mgd1984/boosted-remote/electrical/kicad/boosted_remote.kicad_sch

## KiCad design electrical/kicad/boosted_remote.kicad_sch (2026-04-09)

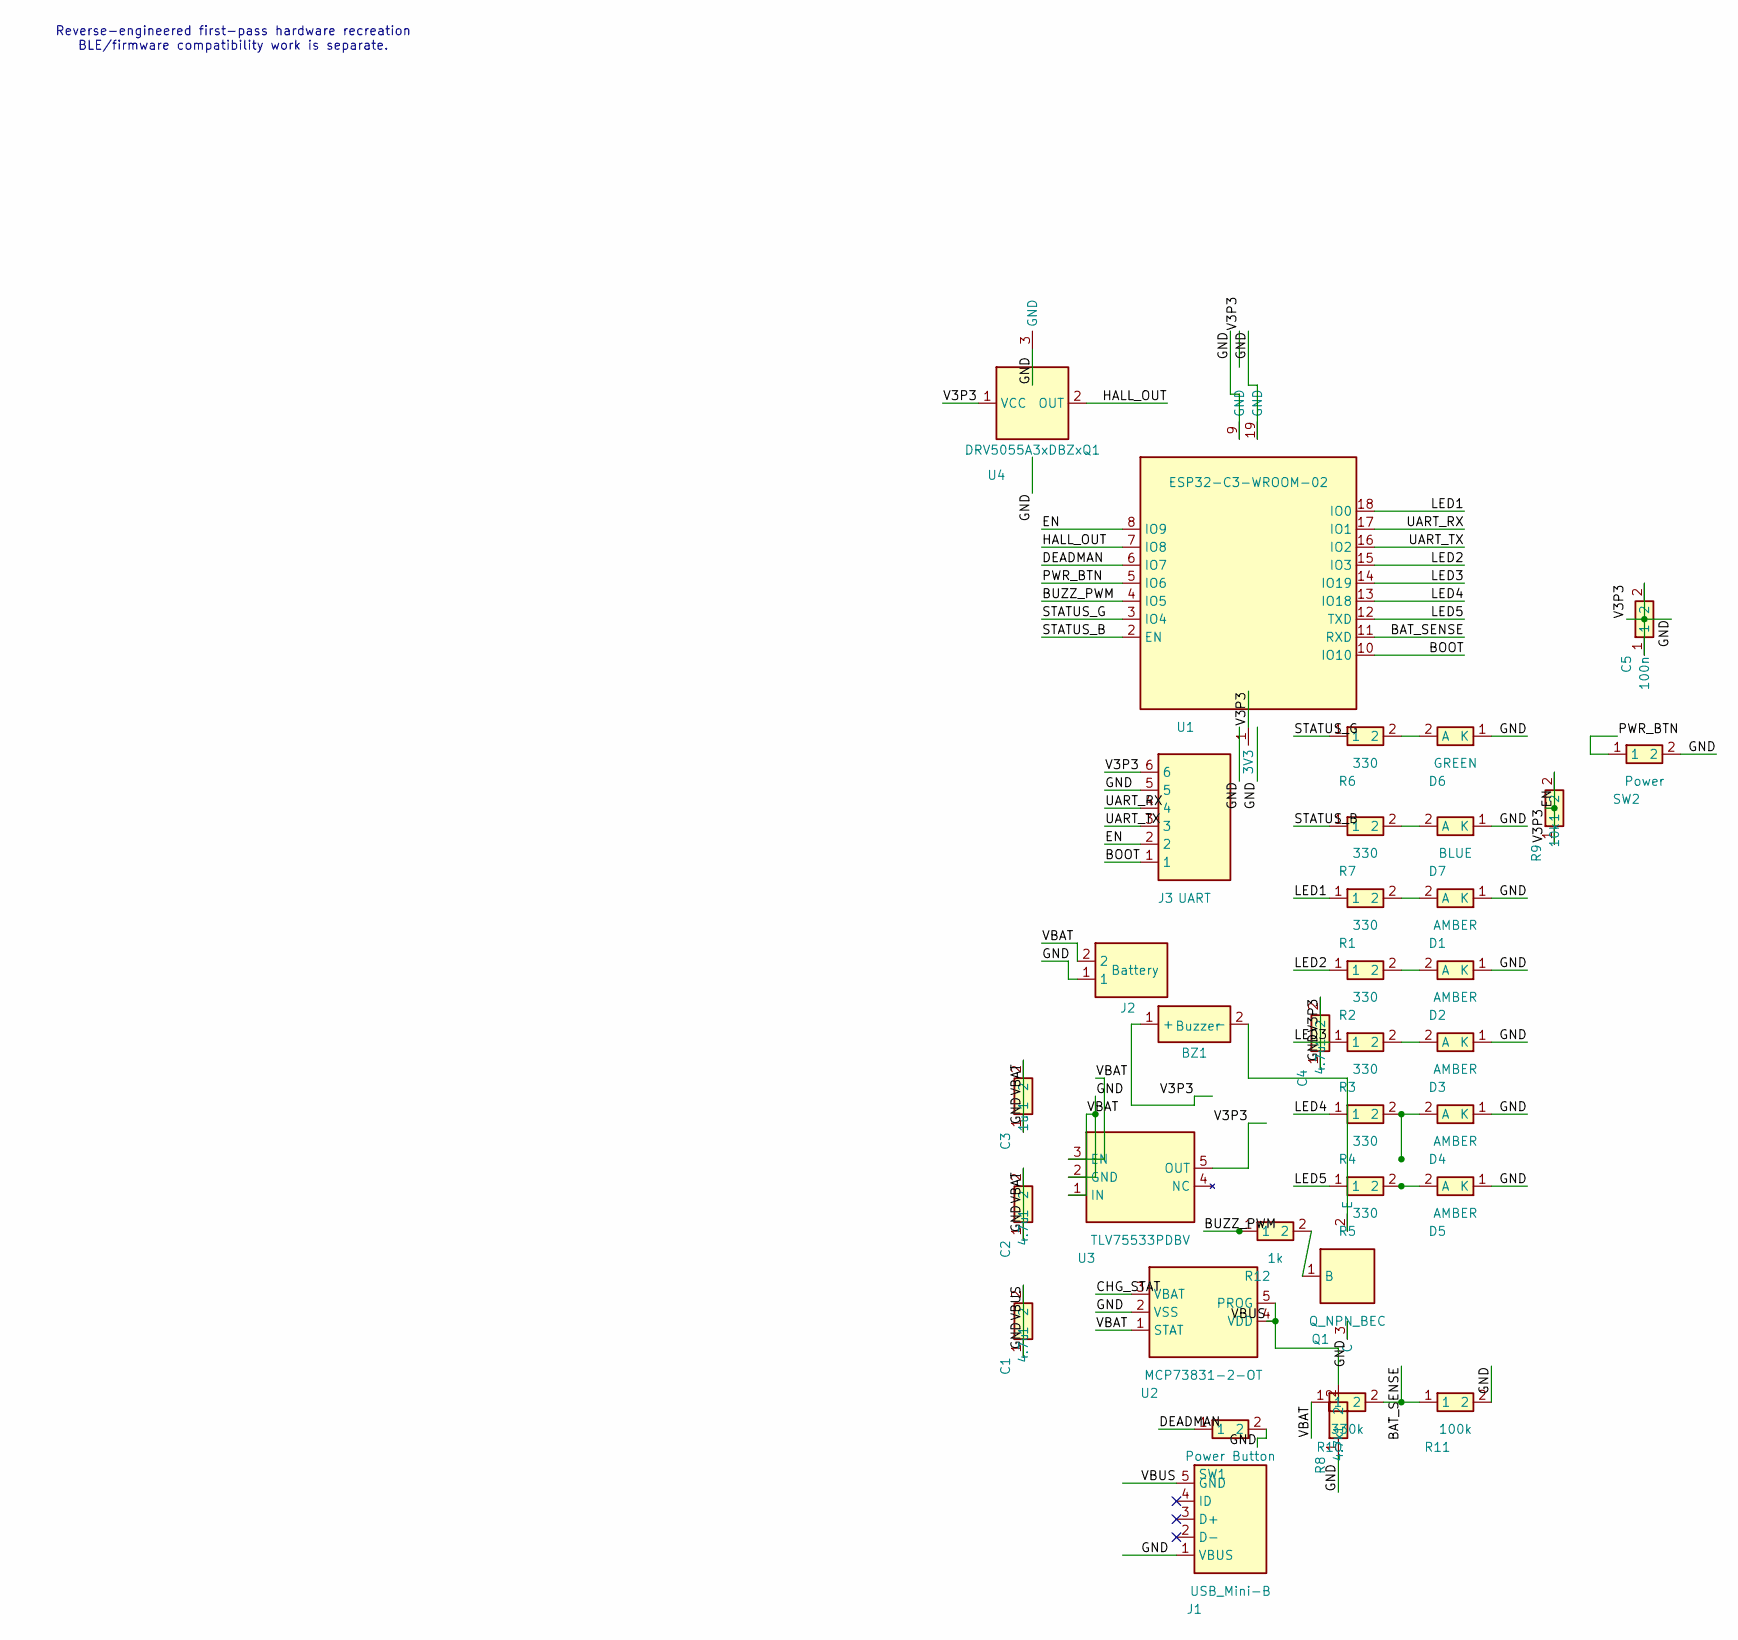
[picture p4: schematic boosted_remote.kicad_sch]

Parts:
BZ1: Buzzer; Buzzer_Murata_PKMCS0909E
C1, C2, C4: 4.7u; C_0603_1608Metric
C3: 1u; C_0603_1608Metric
C5: 100n; C_0603_1608Metric
D1, D2, D3, D4, D5: AMBER; LED_0603_1608Metric
D6: GREEN; LED_0603_1608Metric
D7: BLUE; LED_0603_1608Metric
J1: USB_Mini-B; USB_Mini-B_Lumberg_2486_01_Horizontal
J2: Battery; JST_PH_B2B-PH-K_1x02_P2.00mm_Vertical
J3: UART; PinHeader_1x06_P1.27mm_Vertical
Q1: Q_NPN_BEC; SOT-23
R1, R2, R3, R4, R5, R6, R7: 330; R_0603_1608Metric
R8: 4.7k; R_0603_1608Metric
R9: 10k; R_0603_1608Metric
R10: 330k; R_0603_1608Metric
R11: 100k; R_0603_1608Metric
R12: 1k; R_0603_1608Metric
SW1: Power Button; SW_Push_1P1T-MP_NO_Horizontal_Alps_SKRTLAE010
SW2: Power; SW_SPST_TL3305A
U1: ESP32-C3-WROOM-02
U2: MCP73831-2-OT; SOT-23-5
U3: TLV75533PDBV; SOT-23-5
U4: DRV5055A3xDBZxQ1; SOT-23

Connections:
BAT_SENSE: R10.2, R11.1, U1.11 (RXD)
BOOT: J3.1, U1.10 (IO10)
BUZZ_PWM: R12.1, U1.4 (IO5)
CHG_STAT: U2.3 (VBAT)
DEADMAN: SW1.1, U1.6 (IO7)
EN: BZ1.1 (+), C1.1, C1.2, C2.1, C2.2, C3.1, C3.2, C4.1, C4.2, C5.1, C5.2, D1.1 (K), D2.1 (K), D3.1 (K), D4.1 (K), D5.1 (K), D6.1 (K), D7.1 (K), J1.1 (VBUS), J1.5 (GND), J2.1, J2.2, J3.2, J3.5, J3.6, Q1.3 (C), R8.1, R8.2, R9.1, R9.2, R10.1, R11.2, SW1.2, SW2.2, U1.1 (3V3), U1.8 (IO9), U1.9 (GND), U1.19 (GND), U2.1 (STAT), U2.2 (VSS), U2.4 (VDD), U2.5 (PROG), U3.1 (IN), U3.2 (GND), U3.3 (EN), U3.5 (OUT), U4.1 (VCC), U4.3 (GND)
HALL_OUT: U1.7 (IO8), U4.2 (OUT)
LED1: R1.1, U1.18 (IO0)
LED2: R2.1, U1.15 (IO3)
LED3: R3.1, U1.14 (IO19)
LED4: R4.1, U1.13 (IO18)
LED5: R5.1, U1.12 (TXD)
unnamed: BZ1.2 (-), Q1.2 (E)
unnamed: D1.2 (A), R1.2
unnamed: D2.2 (A), R2.2
unnamed: D3.2 (A), R3.2
unnamed: D4.2 (A), R4.2
unnamed: D5.2 (A), R5.2
unnamed: D6.2 (A), R6.2
unnamed: D7.2 (A), R7.2
unnamed: Q1.1 (B), R12.2
PWR_BTN: SW2.1, U1.5 (IO6)
STATUS_B: R7.1, U1.2 (EN)
STATUS_G: R6.1, U1.3 (IO4)
UART_RX: J3.4, U1.17 (IO1)
UART_TX: J3.3, U1.16 (IO2)

Notes on the sheet:
Reverse-engineered first-pass hardware recreation BLE/firmware compatibility work is separate.
